niubit/piconsole/pcb/images/ssd1309_3.png

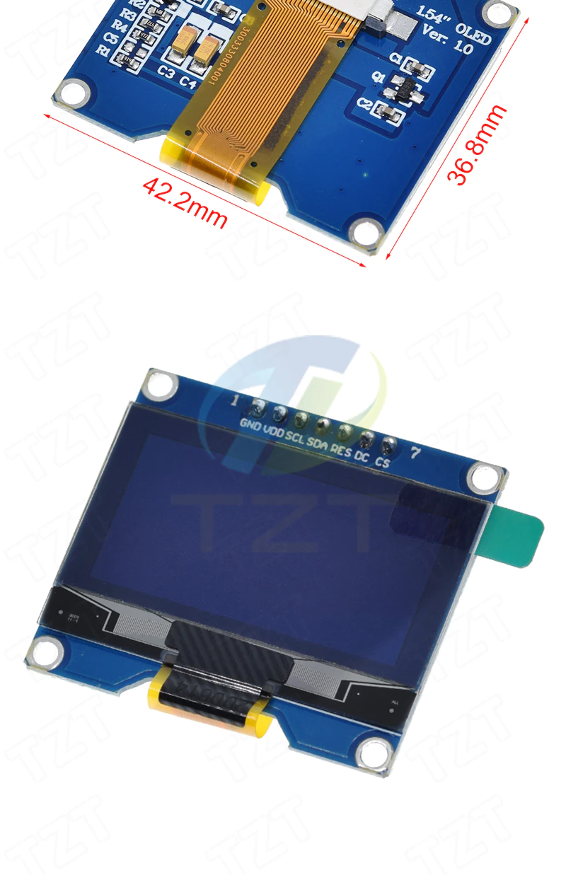
pcb/images/ssd1309_3.png
