niubit/piconsole/pcb/pdf/oled_096.png

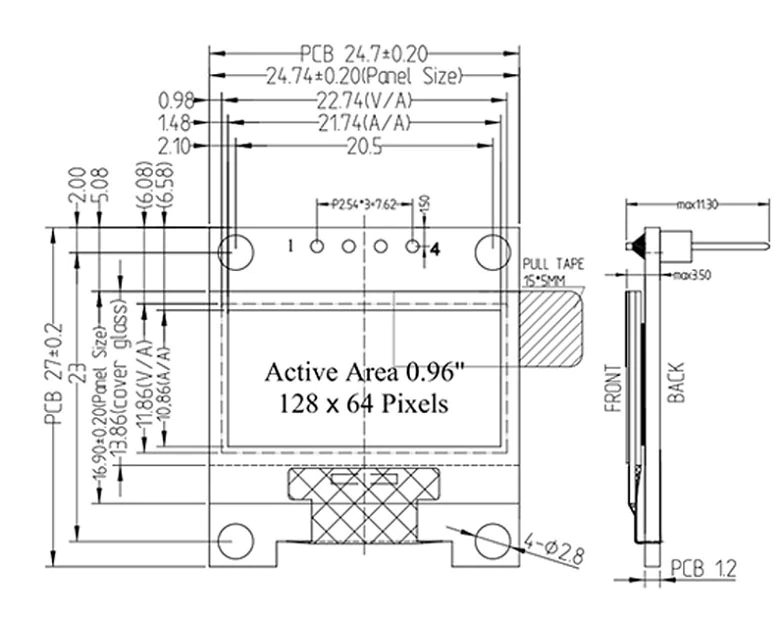
pcb/pdf/oled_096.png
