niubit/piconsole/pcb/pdf/oled_154.png

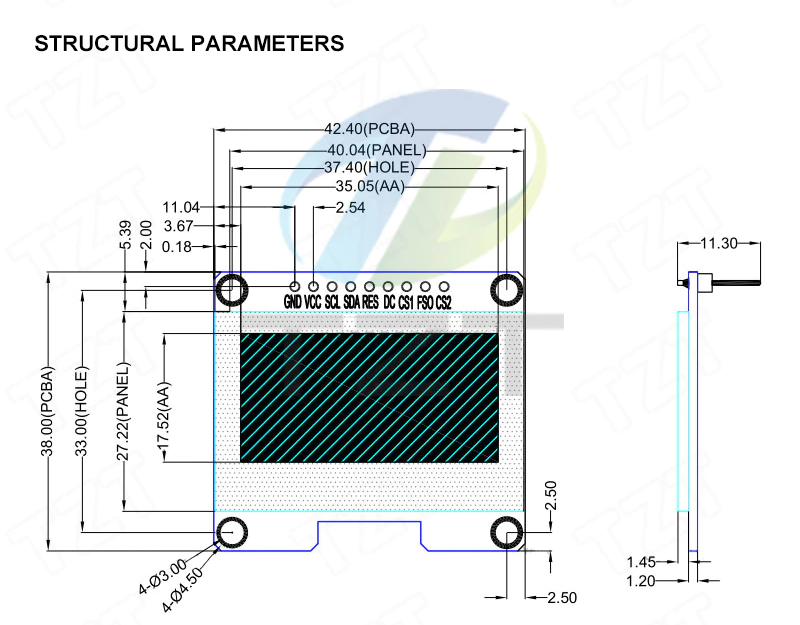
pcb/pdf/oled_154.png
