niubit/piconsole/pcb/pdf/pulsador.png

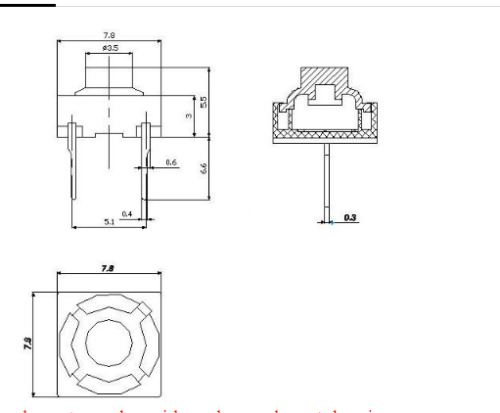
pcb/pdf/pulsador.png
