niubit/piconsole/soft/chip-8_emulator/font.py

"""
Módulo que define los caracteres estándar del sistema.
Los caracteres son de 4x5 píxeles.
Cada línea debe tener un byte de ancho, por lo que se completan con 0.
Ej:
        0:
            ####  =  1111  =  F0
            #  #  =  1001  =  90
            #  #  =  1001  =  90
            #  #  =  1001  =  90
            ####  =  1111  =  F0
Cada carácter tiene 5 bytes de longitud, por tanto para localizar el
carácter 'B' por ejemplo hay que usar DATA[CHAR_SIZE * 0xB]
"""

CHAR_SIZE = 5

DATA = [0xF0, 0x90, 0x90, 0x90, 0xF0, # 0
        0x20, 0x60, 0x20, 0x20, 0x70, # 1
        0xF0, 0x10, 0xF0, 0x80, 0xF0, # 2
        0xF0, 0x10, 0xF0, 0x10, 0xF0, # 3
        0x90, 0x90, 0xF0, 0x10, 0x10, # 4
        0xF0, 0x80, 0xF0, 0x10, 0xF0, # 5
        0xF0, 0x80, 0xF0, 0x90, 0xF0, # 6
        0xF0, 0x10, 0x20, 0x40, 0x40, # 7
        0xF0, 0x90, 0xF0, 0x90, 0xF0, # 8
        0xF0, 0x90, 0xF0, 0x10, 0xF0, # 9
        0xF0, 0x90, 0xF0, 0x90, 0x90, # A
        0xE0, 0x90, 0xE0, 0x90, 0xE0, # B
        0xF0, 0x80, 0x80, 0x80, 0xF0, # C
        0xE0, 0x90, 0x90, 0x90, 0xE0, # D
        0xF0, 0x80, 0xF0, 0x80, 0xF0, # E
        0xF0, 0x80, 0xF0, 0x80, 0x80] # F
